hover-stop/hardware/41464/41464 Friction Cam Lever, Drum Brake, 3D-Printed v6.step

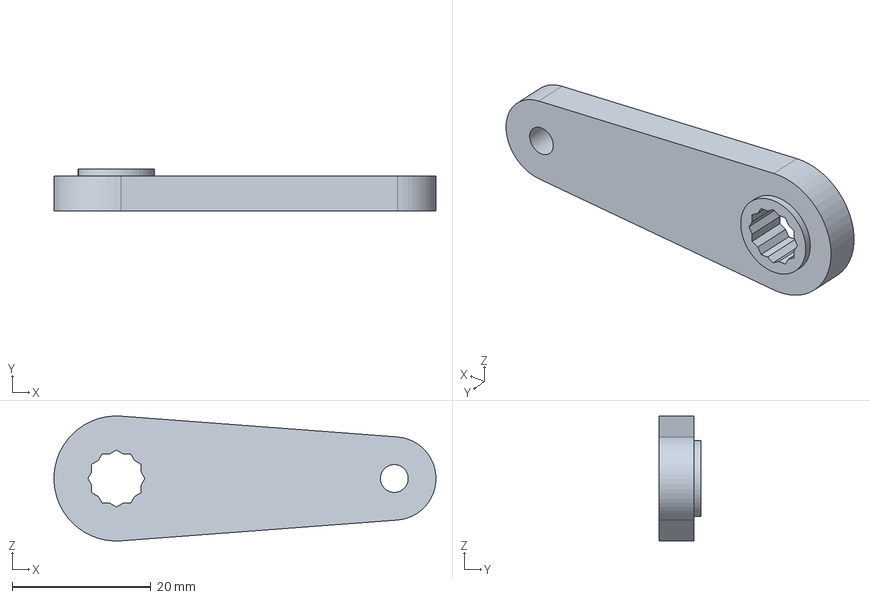
[picture p17: CAD file, 2025-05-27]
41464/41464 Friction Cam Lever, Drum Brake, 3D-Printed v6.step
55.0 x 6.00 x 18.0 mm
