hover-stop/hardware/42807/42807 Case Adapter.step

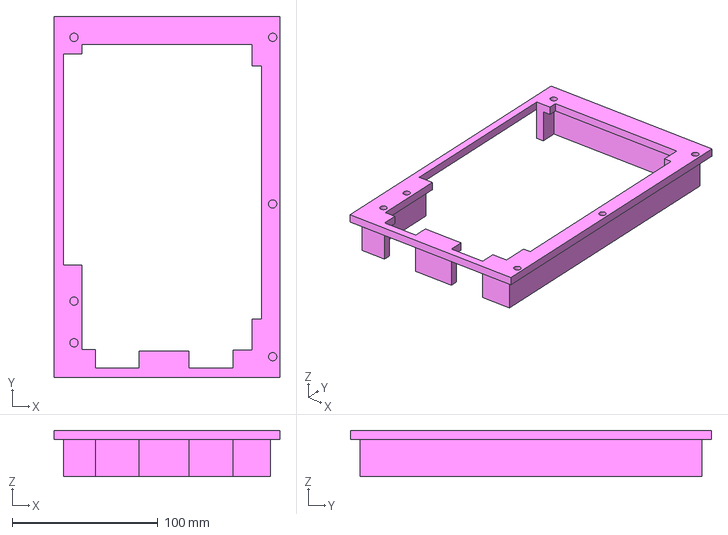
[picture p18: CAD file, 2025-05-23]
42807/42807 Case Adapter.step
154.8 x 247.7 x 31.8 mm
