hover-stop/hardware/48793/48793 Spur Gear, 66 T, Drum Brake.step

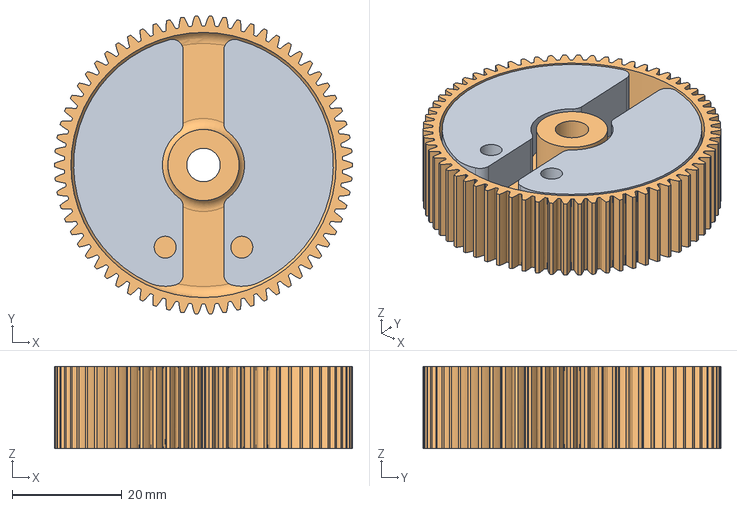
[picture p19: CAD file, 2025-05-27]
48793/48793 Spur Gear, 66 T, Drum Brake.step
54.4 x 54.4 x 15.0 mm
