hover-stop/hardware/57833/57833 Throttle Grip Analog Stick Backing Plate.step

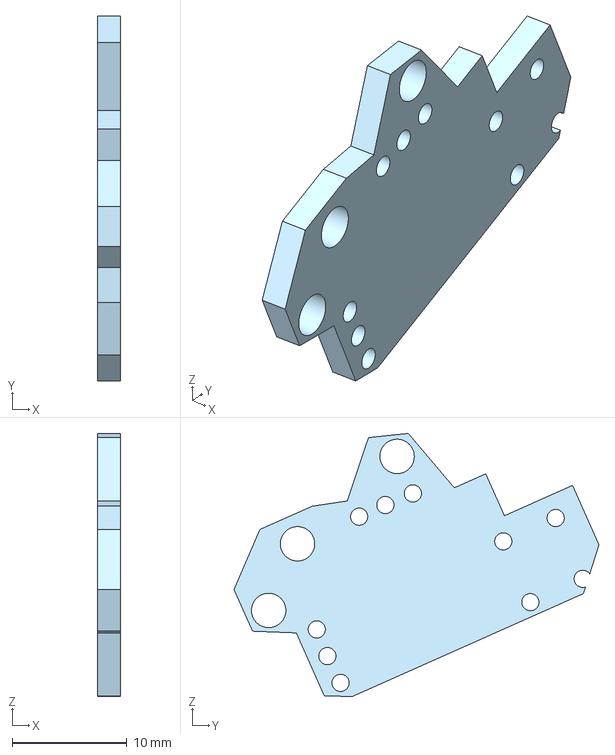
[picture p20: CAD file, 2025-05-27]
57833/57833 Throttle Grip Analog Stick Backing Plate.step
2.00 x 31.8 x 22.9 mm
